andrewzamansky-ucpojects/irrigation_stm32f103/kicad/irrigation_stm32f103/irrigation_stm32f103.kicad_sch

## KiCad design kicad/irrigation_stm32f103/irrigation_stm32f103.kicad_sch (2023-06-05)

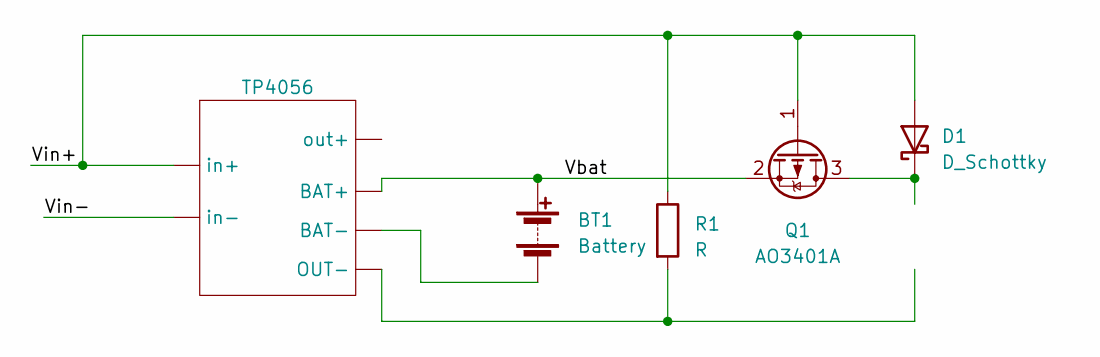
[picture p9: schematic irrigation_stm32f103.kicad_sch]

Parts:
BT1: Battery
D1: D_Schottky
Q1: AO3401A; SOT-23
R1: R
TP4056: (no value)

Connections:
unnamed: BT1.2 (-), TP4056.
unnamed: D1.1 (K), Q1.3 (D)
unnamed: R1.2, TP4056.
Vbat: BT1.1 (+), Q1.2 (S), TP4056.
Vin+: D1.2 (A), Q1.1 (G), R1.1, TP4056.
Vin-: TP4056.
